Metaby/Displayboard/Firmware/GPU/gpu/src/Extern/dallas_one_wire.h

/*
 * An AVR library for communication on a Dallas 1-Wire bus.
 *
 * The main documentation is in dallas_one_wire.c.
 */
 
/******************************************************************************
 * Copyright © 2010, Mike Roddewig (mike@dietfig.org).
 * All rights reserved.
 *
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
 * You should have received a copy of the GNU General Public License
 * along with this program.  If not, see <http://www.gnu.org/licenses/>.
******************************************************************************/

#ifndef DALLAS_ONE_WIRE_H
#define DALLAS_ONE_WIRE_H

/////////////
// Defines //
/////////////

// AVR clock frequency
#define F_CPU 20000000UL // 1 MHz

// Pin defines

#define DALLAS_PORT 	PORTD
#define DALLAS_PORT_IN 	PIND
#define DALLAS_DDR 	DDRD
#define DALLAS_PIN 	5

// The number of devices on the bus.
#define DALLAS_NUM_DEVICES 1

// The number of bits in an identifier.
#define DALLAS_NUM_IDENTIFIER_BITS 64

// One Wire Commands

#define MATCH_ROM_COMMAND 	0x55
#define SKIP_ROM_COMMAND	0xCC
#define SEARCH_ROM_COMMAND 	0xF0

////////////////
// Structures //
////////////////

typedef struct {
	uint8_t identifier[DALLAS_NUM_IDENTIFIER_BITS / 8];
} DALLAS_IDENTIFIER_t;

typedef struct {
	DALLAS_IDENTIFIER_t identifiers[DALLAS_NUM_DEVICES];
	uint8_t num_devices;
} DALLAS_IDENTIFIER_LIST_t;

///////////////
// Functions //
///////////////

// Writes the LSB of the argument to the bus.
void dallas_write(uint8_t);

// Write a byte to the bus.
void dallas_write_byte(uint8_t);

// Write the specified number of bytes to the bus from the supplied buffer.
void dallas_write_buffer(uint8_t * buffer, uint8_t buffer_length);

// Read a bit from the bus and returns it as the LSB.
uint8_t dallas_read(void);

// Reads a byte from the bus.
uint8_t dallas_read_byte(void);

// Reads the specified number of bytes from the bus into the supplied buffer.
void dallas_read_buffer(uint8_t * buffer, uint8_t buffer_length);

// Resets the bus. Returns...
// 1 - if a device or devices indicate presence
// 0 - otherwise
uint8_t dallas_reset(void);

// Powers the bus from the AVR (max 40 mA).
void dallas_drive_bus(void);

// Sends a MATCH ROM command to the specified device. Automatically resets the
// bus.
void dallas_match_rom(DALLAS_IDENTIFIER_t *);

// Sends a SKIP ROM command. Automatically resets the bus.
void dallas_skip_rom(void);

// Populates the identifier list. Returns...
// 0 - if devices were found and there was no error
// 1 - if there was a bus error
// 2 - if there were more devices than specified by DALLAS_NUM_DEVICES
uint8_t dallas_search_identifiers(void);

// Returns the list of identifiers.
DALLAS_IDENTIFIER_LIST_t * get_identifier_list(void);

#endif
