Metaby/Displayboard/Firmware/GPU/gpu/src/os/Programs/serial_listener.h

/*
 * serial_listener.h
 *
 * Created: 08.04.2017 13:43:22
 *  Author: Max Brand
 */ 

#include "../../GraphicsDriver/Display.h"
#include "../../Tools/Tools.h"

#ifndef SERIAL_LISTENER_H_
#define SERIAL_LISTENER_H_

#define SERIAL_BUFFER_SIZE 22

uint8_t serial_listener_fnct();

#endif /* SERIAL_LISTENER_H_ */
