Metaby/Displayboard/Firmware/GPU/gpu/src/os/Programs/count_down.h

/*
 * count_down.h
 *
 * Created: 01.02.2016 07:10:45
 *  Author: Max
 */ 


#ifndef COUNT_DOWN_H_
#define COUNT_DOWN_H_

#include "../../GraphicsDriver/Display.h"

uint8_t count;

uint8_t count_down_fnct();

#endif /* COUNT_DOWN_H_ */
