Metaby/Displayboard/Firmware/GPU/gpu/src/os/Programs/hello_world.h

/*
 * hello_world.h
 *
 * Created: 01.02.2016 00:06:11
 *  Author: Max
 */ 

#include "../../GraphicsDriver/Display.h"
#include "../../Tools/Tools.h"

#ifndef HELLO_WORLD_H_
#define HELLO_WORLD_H_

uint8_t hello_world_fnct();

#endif /* HELLO_WORLD_H_ */
