Metaby/Displayboard/Firmware/GPU/gpu/src/os/Programs/gfx_test.h

/*
 * gfx_test.h
 *
 * Created: 05.02.2016 00:27:28
 *  Author: Max
 */ 

#include "../../GraphicsDriver/Display.h"
#include "../../Tools/Tools.h"
#include "../Kernel.h"

#ifndef GFX_TEST_H_
#define GFX_TEST_H_

uint8_t gfx_test_fnct();
void timer_fnct();

#endif /* GFX_TEST_H_ */
